hhuysqt/esp32s3-keyboard/hardware/kicad_proj/esp32_keyboard-v0.1.sch

## KiCad design hardware/kicad_proj/esp32_keyboard-v0.1.sch (2023-02-06)

Schematic: esp32_keyboard-v0.1.sch

Parts:
BT1: Battery; PinHeader_1x02_P2.54mm_Vertical
C1, C9: 1u; C_0603_1608Metric
C2, C3, C4, C5, C8: 10u; C_0603_1608Metric
C6, C7: 12.5p; C_0603_1608Metric
D1: RED; LED_0603_1608Metric
D2: GREEN; LED_0603_1608Metric
D3, D4: D_Small_ALT; D_SOD-123
J1: USB_EXT; PinHeader_1x04_P2.54mm_Vertical
J2: Debug; PinHeader_1x04_P2.54mm_Vertical
P1: USB_C_USB2.0; USB_C_Receptacle_HRO_TYPE-C-31-M-12
R1, R2, R3, R4, R5, R6, R9, R10, R11: 1.2k; R_0603_1608Metric
R7: 100; R_0603_1608Metric
R8, R12: 10k; R_0603_1608Metric
R13: 15k; R_0603_1608Metric
SW1: SW_SPDT; MSK22D14G2-SWITCH
U1: Keyboard-40p; Keyboard-40
U2: Trackpoint-12p; Trackpad-12p
U3: Keyboard-30p; TE_3-84952-0_1x30-1MP_P1.0mm_Horizontal
U4: Trackpoint-10p; TE_1-84952-0_1x10-1MP_P1.0mm_Horizontal
U5: 74LS138; SSOP-16_4.4x5.2mm_P0.65mm
U6: ESP32-S3-WROOM-1
U7: TP4056; SOP-8_3.9x4.9mm_P1.27mm
U8: XC6206PxxxMR; SOT-23
U9: Keyboard-36p; Keyboard-36
Y1: 32k; Crystal_SMD_MicroCrystal_CC7V-T1A-2Pin_3.2x1.5mm

Notes on the sheet:
Rprog Charge Current 1.2K 1A 2K 580mA
Thinkpad E580
Thinkpad T470
Thinkpad E430/E530
Thinkpad E580/T470
Keyboard Connector
ESP32-S3- WROOM-1
Trackpoint
Column Select
ESP32-S3 USB/BLE Keyboard Driver
Power
