hhuysqt/esp32s3-keyboard/components/tinyusb/additions/include/tusb_config.h

/*
 * The MIT License (MIT)
 *
 * Copyright (c) 2019 Ha Thach (tinyusb.org),
 * Additions Copyright (c) 2020, Espressif Systems (Shanghai) PTE LTD
 *
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
 */

#pragma once

#include "tusb_option.h"
#include "sdkconfig.h"

#ifdef __cplusplus
extern "C" {
#endif

#ifndef CONFIG_TINYUSB_CDC_ENABLED
#   define CONFIG_TINYUSB_CDC_ENABLED 0
#   define CONFIG_TINYUSB_CDC_PORT_NUM 0
#endif

#ifndef CONFIG_TINYUSB_MSC_ENABLED
#   define CONFIG_TINYUSB_MSC_ENABLED 0
#endif

#ifndef CONFIG_TINYUSB_HID_ENABLED
#   define CONFIG_TINYUSB_HID_ENABLED 0
#endif

#ifndef CONFIG_TINYUSB_MIDI_ENABLED
#   define CONFIG_TINYUSB_MIDI_ENABLED 0
#endif

#ifndef CONFIG_TINYUSB_CUSTOM_CLASS_ENABLED
#   define CONFIG_TINYUSB_CUSTOM_CLASS_ENABLED 0
#endif

#define CFG_TUSB_RHPORT0_MODE       OPT_MODE_DEVICE | OPT_MODE_FULL_SPEED
#define CFG_TUSB_OS                 OPT_OS_FREERTOS

/* USB DMA on some MCUs can only access a specific SRAM region with restriction on alignment.
 * Tinyusb use follows macros to declare transferring memory so that they can be put
 * into those specific section.
 * e.g
 * - CFG_TUSB_MEM SECTION : __attribute__ (( section(".usb_ram") ))
 * - CFG_TUSB_MEM_ALIGN   : __attribute__ ((aligned(4)))
 */
#ifndef CFG_TUSB_MEM_SECTION
#   define CFG_TUSB_MEM_SECTION
#endif

#ifndef CFG_TUSB_MEM_ALIGN
#   define CFG_TUSB_MEM_ALIGN       TU_ATTR_ALIGNED(4)
#endif

#ifndef CFG_TUD_ENDPOINT0_SIZE
#define CFG_TUD_ENDPOINT0_SIZE      64
#endif

// CDC FIFO size of TX and RX
#define CFG_TUD_CDC_RX_BUFSIZE      CONFIG_TINYUSB_CDC_RX_BUFSIZE
#define CFG_TUD_CDC_TX_BUFSIZE      CONFIG_TINYUSB_CDC_TX_BUFSIZE

// MSC Buffer size of Device Mass storage
#define CFG_TUD_MSC_BUFSIZE         CONFIG_TINYUSB_MSC_BUFSIZE

// HID buffer size Should be sufficient to hold ID (if any) + Data
#define CFG_TUD_HID_BUFSIZE         CONFIG_TINYUSB_HID_BUFSIZE

// Enabled device class driver
#define CFG_TUD_CDC                 CONFIG_TINYUSB_CDC_PORT_NUM
#define CFG_TUD_MSC                 CONFIG_TINYUSB_MSC_ENABLED
#define CFG_TUD_HID                 CONFIG_TINYUSB_HID_ENABLED
#define CFG_TUD_MIDI                CONFIG_TINYUSB_MIDI_ENABLED
#define CFG_TUD_CUSTOM_CLASS        CONFIG_TINYUSB_CUSTOM_CLASS_ENABLED

#define CFG_TUD_HID_EP_BUFSIZE 9

#ifdef __cplusplus
}
#endif
