hhuysqt/esp32s3-keyboard/main/keymap-e580.c

/**
 * This file is part of esp32s3-keyboard.
 *
 * Copyright (C) 2020-2021 Yuquan He <heyuquan20b at ict dot ac dot cn> 
 * (Institute of Computing Technology, Chinese Academy of Sciences)
 *
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
 * You should have received a copy of the GNU General Public License
 * along with esp32s3-keyboard. If not, see <http://www.gnu.org/licenses/>.
 */

/**
 * Keymap for Thinkpad E580/T470 etc.
 */

#include "keymap.h"

keytable_t kbtbl[] = {
  { 0,  1, 0, KEY_ESC },
  { 7,  4, 0, KEY_F1  },
  { 7,  3, 0, KEY_F2  },
  { 1,  3, 0, KEY_F3  },
  { 0,  3, 0, KEY_F4  },
  { 0, 14, 0, KEY_F5  },
  { 0,  8, 0, KEY_F6  },
  { 1,  6, 0, KEY_F7  },
  { 7,  6, 0, KEY_F8  },
  { 7, 14, 0, KEY_F9  },
  { 5, 14, 0, KEY_F10 },
  { 5, 13, 0, KEY_F11 },
  { 5, 11, 0, KEY_F12 },
  { 7, 12, 0, KEY_HOME },
  { 5, 12, 0, KEY_END },
  { 7, 11, 0, KEY_INSERT },
  { 7, 13, 0, KEY_DELETE },

  { 7,  1, '~', KEY_GRAVE },
  { 5,  1, '1', KEY_1 },
  { 5,  4, '2', KEY_2 },
  { 5,  3, '3', KEY_3 },
  { 5,  5, '4', KEY_4 },
  { 7,  5, '5', KEY_5 },
  { 7,  2, '6', KEY_6 },
  { 5,  2, '7', KEY_7 },
  { 5,  8, '8', KEY_8 },
  { 5,  6, '9', KEY_9 },
  { 5,  7, '0', KEY_0 },
  { 7,  7, '-', KEY_MINUS },
  { 7,  8, '=', KEY_EQUAL },
  { 1, 14, 0, KEY_BACKSPACE },

  { 1,  1, 0, KEY_TAB },
  { 6,  1, 'q', KEY_Q },
  { 6,  4, 'w', KEY_W },
  { 6,  3, 'e', KEY_E },
  { 6,  5, 'r', KEY_R },
  { 1,  5, 't', KEY_T },
  { 1,  2, 'y', KEY_Y },
  { 6,  2, 'u', KEY_U },
  { 6,  8, 'i', KEY_I },
  { 6,  6, 'o', KEY_O },
  { 6,  7, 'p', KEY_P },
  { 1,  7, '[', KEY_LEFTBRACE },
  { 1,  8, ']', KEY_RIGHTBRACE },
  { 4, 14, '\\', KEY_BACKSLASH },

  { 1,  4, 0, KEY_CAPSLOCK },
  { 4,  1, 'a', KEY_A },
  { 4,  4, 's', KEY_S },
  { 4,  3, 'd', KEY_D },
  { 4,  5, 'f', KEY_F },
  { 0,  5, 'g', KEY_G },
  { 0,  2, 'h', KEY_H },
  { 4,  2, 'j', KEY_J },
  { 4,  8, 'k', KEY_K },
  { 4,  6, 'l', KEY_L },
  { 4,  7, ';', KEY_SEMICOLON },
  { 0,  7, '\'', KEY_APOSTROPHE },
  { 3, 14, 0, KEY_ENTER },

  { 1,  0, 0, KEY_LEFTSHIFT },
  { 3,  1, 'z', KEY_Z },
  { 3,  4, 'x', KEY_X },
  { 3,  3, 'c', KEY_C },
  { 3,  5, 'v', KEY_V },
  { 2,  5, 'b', KEY_B },
  { 2,  2, 'n', KEY_N },
  { 3,  2, 'm', KEY_M },
  { 3,  8, ',', KEY_COMMA },
  { 3,  6, '.', KEY_DOT },
  { 2,  7, '/', KEY_SLASH },
  { 3,  0, 0, KEY_RIGHTSHIFT },

  // { 23, 24, 0, 0 }, // Fn key
  { 7,  9, 0, KEY_LEFTCTRL },
  { 1, 11, 0, KEY_LEFTMETA },  // win key
  { 0, 10, 0, KEY_LEFTALT },
  { 2, 14, ' ', KEY_SPACE },
  { 2, 10, 0, KEY_RIGHTALT },
  { 5, 10, 0, KEY_PRTSC },
  { 3,  9, 0, KEY_RIGHTCTRL },
  { 7, 15, 0, KEY_PAGEUP },
  { 0, 12, 0, KEY_UP },
  { 5, 15, 0, KEY_PAGEDOWN },

  { 2, 12, 0, KEY_LEFT },
  { 2, 13, 0, KEY_DOWN },
  { 2, 11, 0, KEY_RIGHT },

  { 1, 12, 0, KEY_MEDIA_CALC },
  { 6, 12, '(', KEY_KPLEFTPAREN },
  { 1, 15, ')', KEY_KPRIGHTPAREN },
  { 6, 15, 0, KEY_BACKSPACE },
  { 0, 16, 0, KEY_NUMLOCK },
  { 1, 16, '/', KEY_KPSLASH },
  { 6, 16, '*', KEY_KPASTERISK },
  { 7, 16, '-', KEY_KPMINUS },
  { 4, 16, '7', KEY_KP7 },
  { 5, 16, '8', KEY_KP8 },
  { 3, 16, '9', KEY_KP9 },
  { 2, 16, '+', KEY_KPPLUS },
  { 0, 17, '4', KEY_KP4 },
  { 1, 17, '5', KEY_KP5 },
  { 6, 17, '6', KEY_KP6 },
  { 7, 17, '1', KEY_KP1 },
  { 4, 17, '2', KEY_KP2 },
  { 5, 17, '3', KEY_KP3 },
  { 3, 17, 0, KEY_KPENTER },
  { 2, 17, '0', KEY_KP0 },
  { 6, 11, '.', KEY_KPDOT },
};

fn_keytable_t fntbl[] = {
  { 0,  1, 0, FN_FNLOCK },
  { 7,  4, KEY_CONSUMER_MUTE, FN_NOP  },
  { 7,  3, KEY_CONSUMER_VOLUME_DECREMENT, FN_NOP  },
  { 1,  3, KEY_CONSUMER_VOLUME_INCREMENT, FN_NOP  },
  // { 0,  3, , 0 },
  { 0, 14, KEY_CONSUMER_BRIGHTNESS_DECREMENT, FN_NOP },
  { 0,  8, KEY_CONSUMER_BRIGHTNESS_INCREMENT, FN_NOP },
  // { 1,  6, , 0 },
  // { 7,  6, , 0 },
  // { 7, 14, , 0 },
  // { 5, 14, , 0 },
  // { 5, 13, , 0 },
  // { 5, 11, , 0 },
  { 2, 14, 0, FN_BACKLIGHT },
};
